ElectroTechnique/TSynth-for-Teensy3.6/sawtoothWave.h

const int16_t sawtoothWavetable[45][257] = {{-0,28053,27402,27407,27049,26921,26644,26460,26226,26008,25800,25562,25370,25120,24936,24681,24499,24245,24060,23810,23620,23377,23178,22945,22736,22512,22294,22080,21853,21646,21413,21211,20975,20774,20537,20337,20101,19898,19666,19459,19231,19019,18797,18579,18363,18139,17928,17700,17492,17262,17056,16824,16618,16388,16180,15952,15741,15516,15302,15081,14863,14646,14424,14211,13985,13775,13547,13338,13110,12901,12673,12463,12237,12025,11801,11586,11365,11147,10930,10709,10494,10270,10058,9832,9622,9395,9184,8958,8747,8521,8309,8086,7870,7650,7432,7214,6993,6778,6555,6342,6117,5905,5679,5468,5242,5031,4806,4593,4370,4154,3934,3716,3498,3277,3062,2839,2626,2401,2189,1964,1752,1526,1315,1090,877,654,439,218,0,-218,-439,-654,-877,-1090,-1315,-1526,-1752,-1964,-2189,-2401,-2626,-2839,-3062,-3277,-3498,-3716,-3934,-4154,-4370,-4593,-4806,-5031,-5242,-5468,-5679,-5905,-6117,-6342,-6555,-6778,-6993,-7214,-7432,-7650,-7870,-8085,-8309,-8521,-8747,-8958,-9184,-9395,-9622,-9832,-10058,-10270,-10494,-10709,-10930,-11147,-11365,-11586,-11801,-12025,-12237,-12463,-12673,-12901,-13110,-13338,-13547,-13775,-13986,-14211,-14424,-14646,-14863,-15081,-15302,-15516,-15741,-15952,-16180,-16388,-16618,-16824,-17056,-17262,-17492,-17700,-17928,-18139,-18363,-18579,-18797,-19019,-19231,-19459,-19666,-19898,-20101,-20337,-20538,-20774,-20975,-21211,-21413,-21646,-21853,-22080,-22294,-22512,-22736,-22945,-23178,-23377,-23620,-23810,-24061,-24245,-24500,-2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
};
