ElectroTechnique/TSynth-for-Teensy3.6/squareWave.h

const int16_t squareWavetable[45][257] = {{0,26004,25608,25811,25687,25766,25718,25743,25735,25729,25746,25721,25752,25717,25754,25717,25753,25719,25750,25723,25745,25728,25740,25733,25735,25737,25731,25741,25728,25744,25726,25745,25726,25744,25727,25743,25729,25740,25732,25737,25735,25734,25738,25731,25741,25729,25742,25728,25742,25728,25742,25729,25740,25731,25738,25734,25735,25736,25733,25739,25730,25741,25729,25742,25728,25742,25729,25741,25730,25739,25733,25736,25735,25734,25738,25731,25740,25729,25742,25728,25742,25728,25742,25729,25741,25731,25738,25734,25735,25737,25732,25740,25729,25743,25727,25744,25726,25745,25726,25744,25728,25741,25731,25737,25735,25733,25740,25728,25745,25723,25750,25719,25753,25717,25754,25717,25752,25721,25746,25729,25735,25743,25718,25766,25687,25811,25608,26004,-3,-26004,-25608,-25811,-25687,-25766,-25718,-25743,-25735,-25729,-25746,-25721,-25752,-25717,-25754,-25717,-25753,-25719,-25750,-25723,-25745,-25728,-25740,-25733,-25735,-25737,-25731,-25741,-25728,-25744,-25726,-25745,-25726,-25744,-25727,-25743,-25729,-25740,-25732,-25737,-25735,-25734,-25738,-25731,-25741,-25729,-25742,-25728,-25742,-25728,-25742,-25729,-25740,-25731,-25738,-25734,-25735,-25736,-25732,-25739,-25730,-25741,-25729,-25742,-25728,-25742,-25729,-25741,-25730,-25739,-25733,-25737,-25735,-25734,-25738,-25731,-25740,-25729,-25742,-25728,-25742,-25728,-25742,-25729,-25741,-25731,-25738,-25734,-25735,-25737,-25732,-25740,-25729,-25743,-25727,-25744,-25726,-25745,-25726,-257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
};
